ThoPhi/DongHoChu_TiengAnh/CircuitBuffer/eagleUp/eagleUp_ShiftCircuit_board_bottom.png

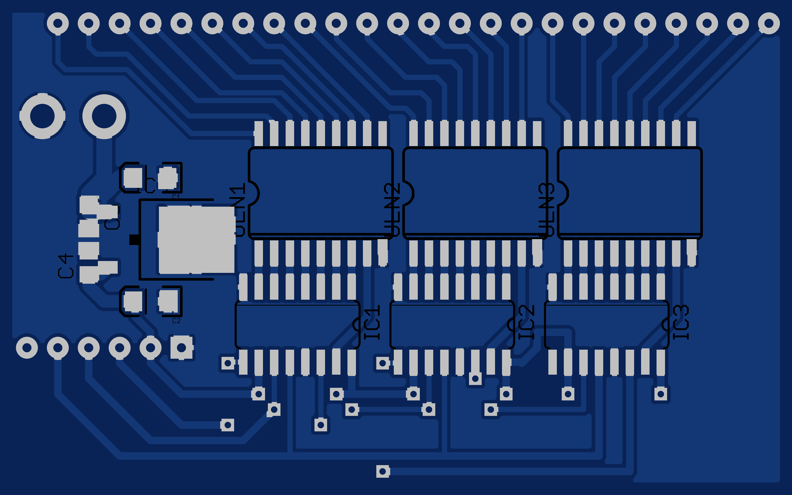
CircuitBuffer/eagleUp/eagleUp_ShiftCircuit_board_bottom.png
