ThoPhi/DongHoChu_TiengAnh/CircuitBuffer/eagleUp/eagleUp_ShiftCircuit_board_top.png

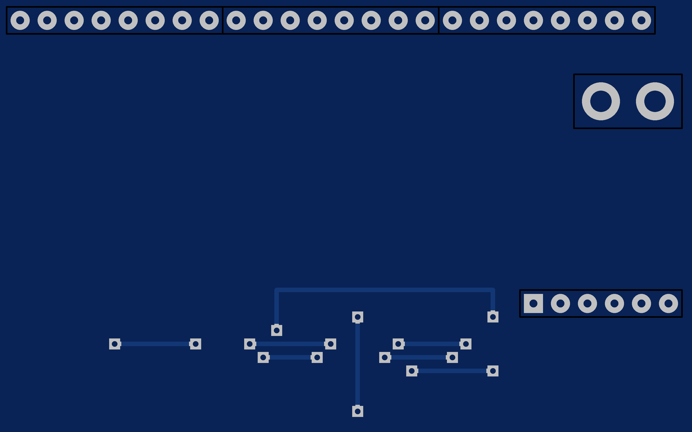
CircuitBuffer/eagleUp/eagleUp_ShiftCircuit_board_top.png
