ThoPhi/DongHoChu_TiengAnh/CircuitBuffer/eagleUp/eagleUp_ShiftCircuit_bottom.png

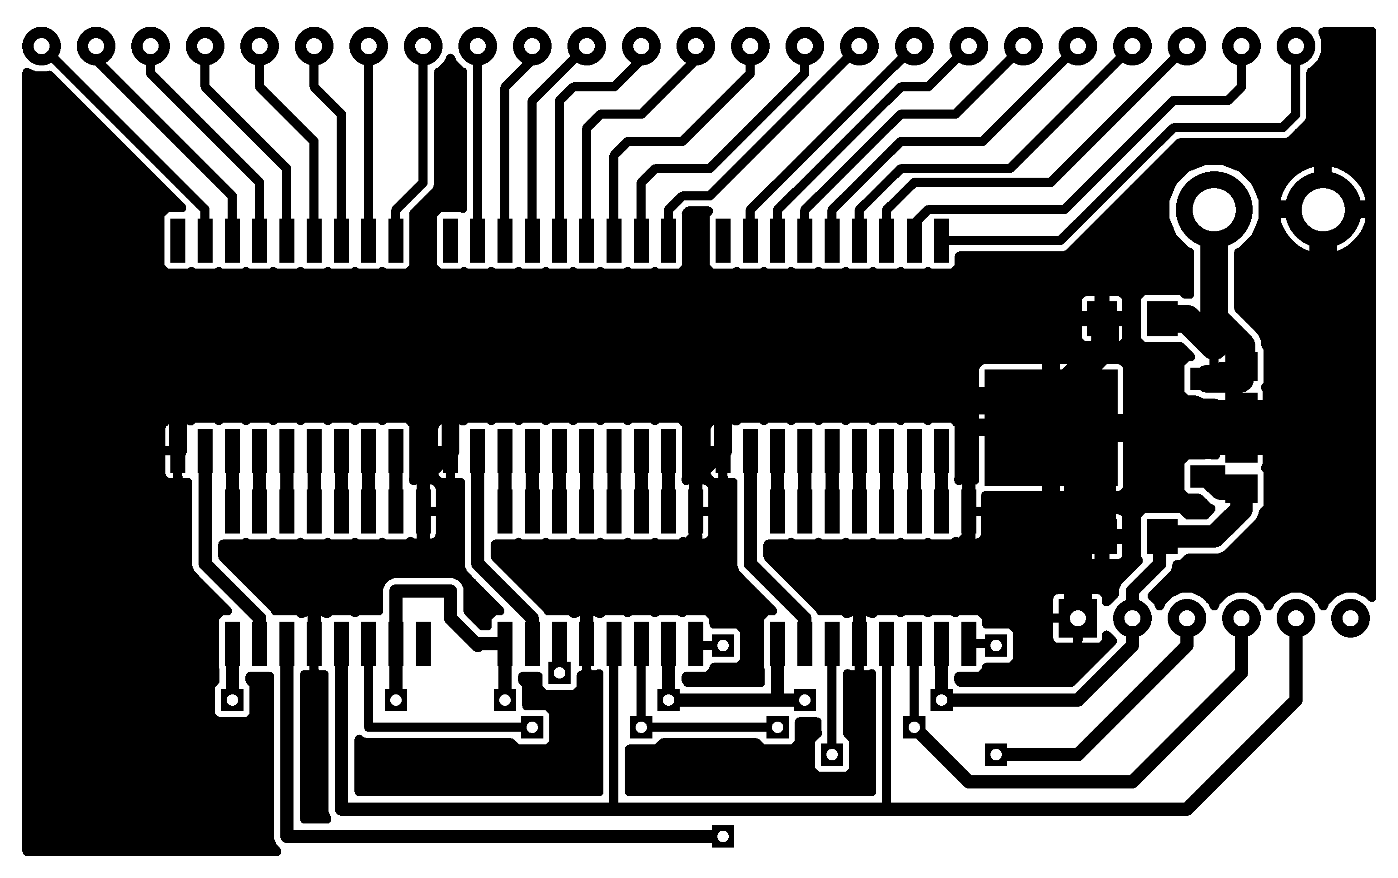
CircuitBuffer/eagleUp/eagleUp_ShiftCircuit_bottom.png
