ThoPhi/DongHoChu_TiengAnh/CircuitBuffer/eagleUp/eagleUp_ShiftCircuit_bottom_mask.png

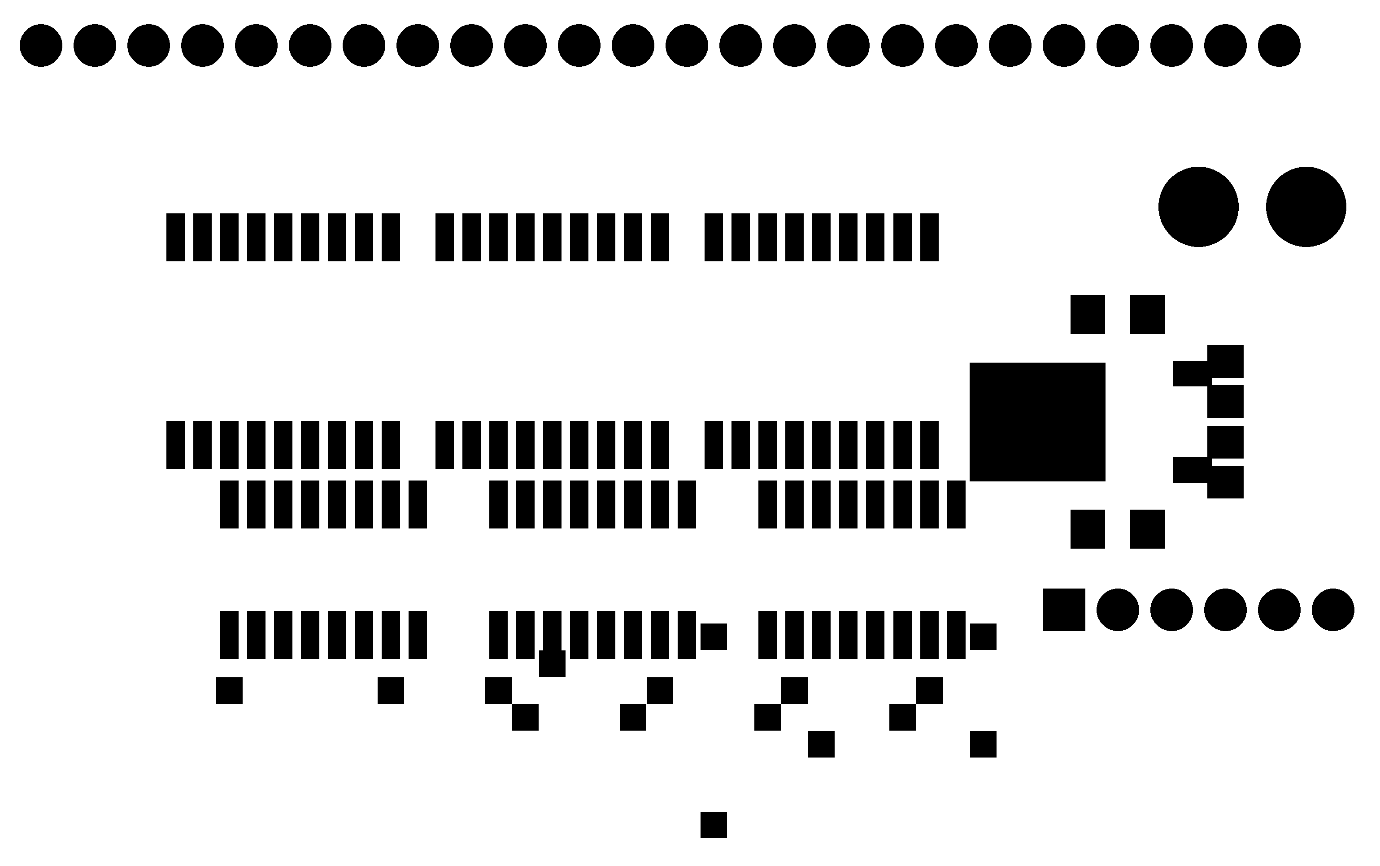
CircuitBuffer/eagleUp/eagleUp_ShiftCircuit_bottom_mask.png
