ThoPhi/DongHoChu_TiengAnh/CircuitBuffer/eagleUp/eagleUp_ShiftCircuit_bottom_silk.png

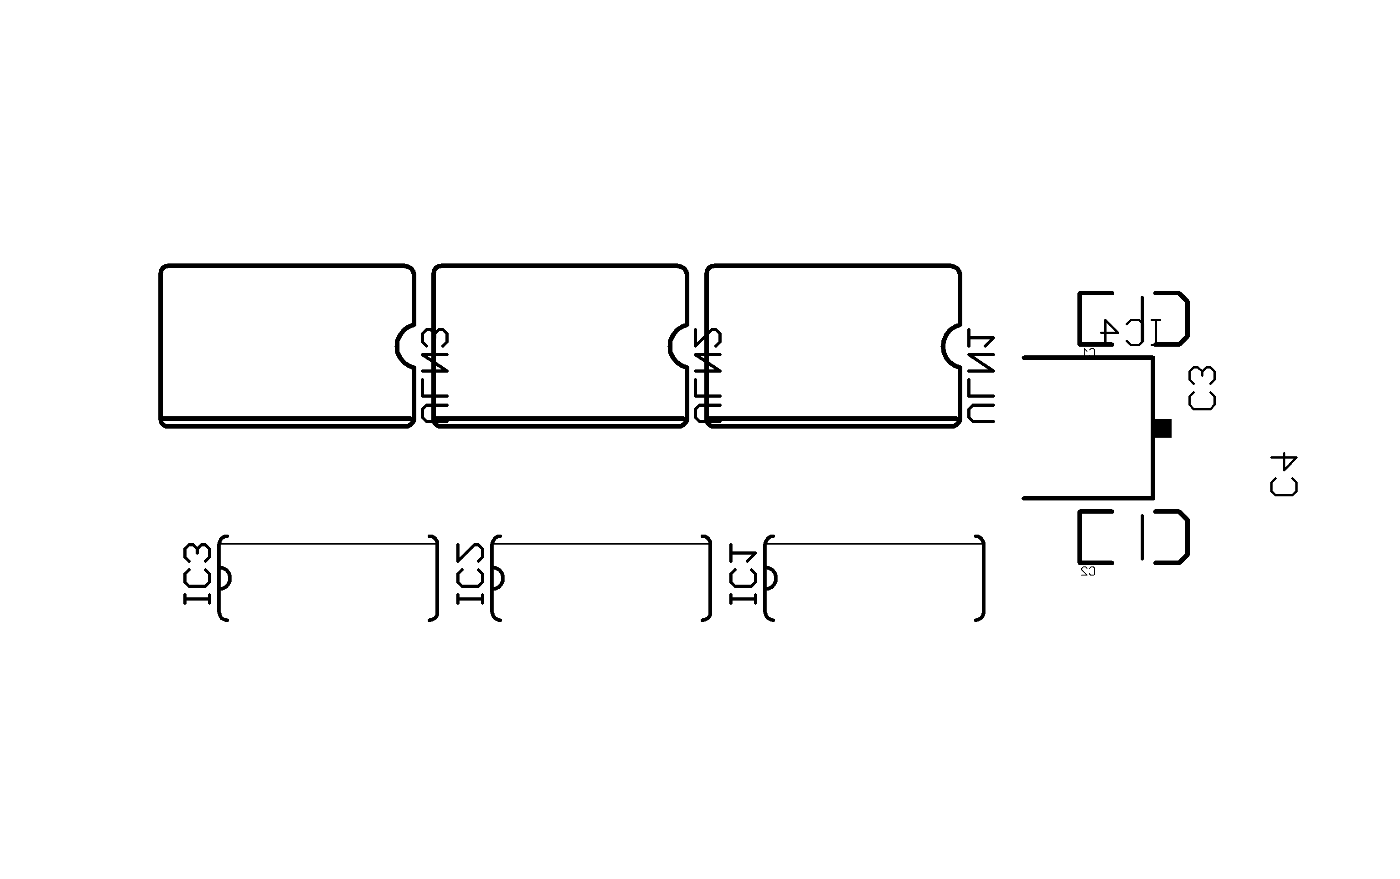
CircuitBuffer/eagleUp/eagleUp_ShiftCircuit_bottom_silk.png
