ThoPhi/DongHoChu_TiengAnh/CircuitBuffer/eagleUp/eagleUp_ShiftCircuit_imagesize.png

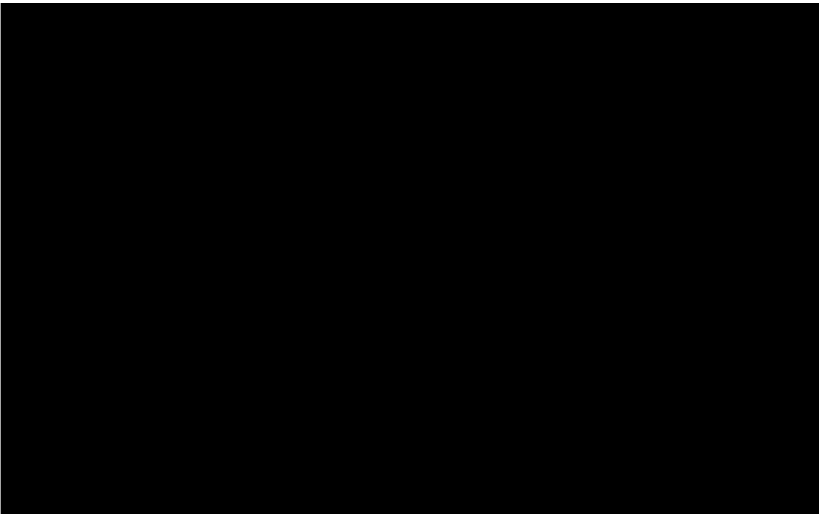
CircuitBuffer/eagleUp/eagleUp_ShiftCircuit_imagesize.png
