ThoPhi/DongHoChu_TiengAnh/CircuitBuffer/eagleUp/eagleUp_ShiftCircuit_outline.png

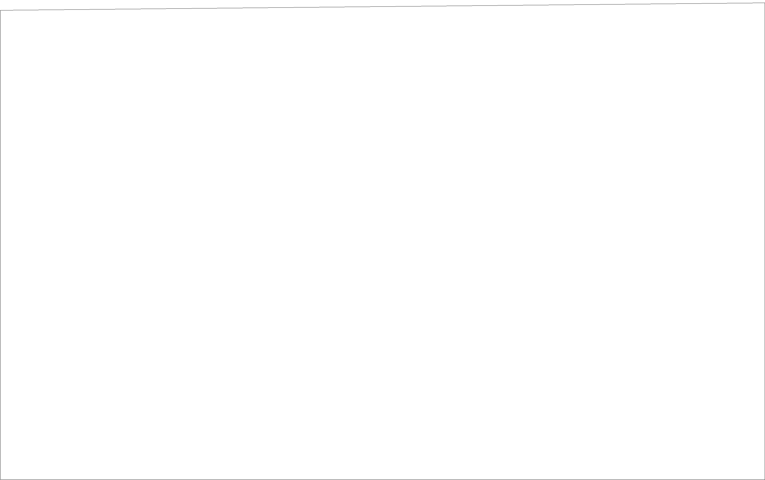
CircuitBuffer/eagleUp/eagleUp_ShiftCircuit_outline.png
