ThoPhi/DongHoChu_TiengAnh/CircuitBuffer/eagleUp/eagleUp_ShiftCircuit_top.png

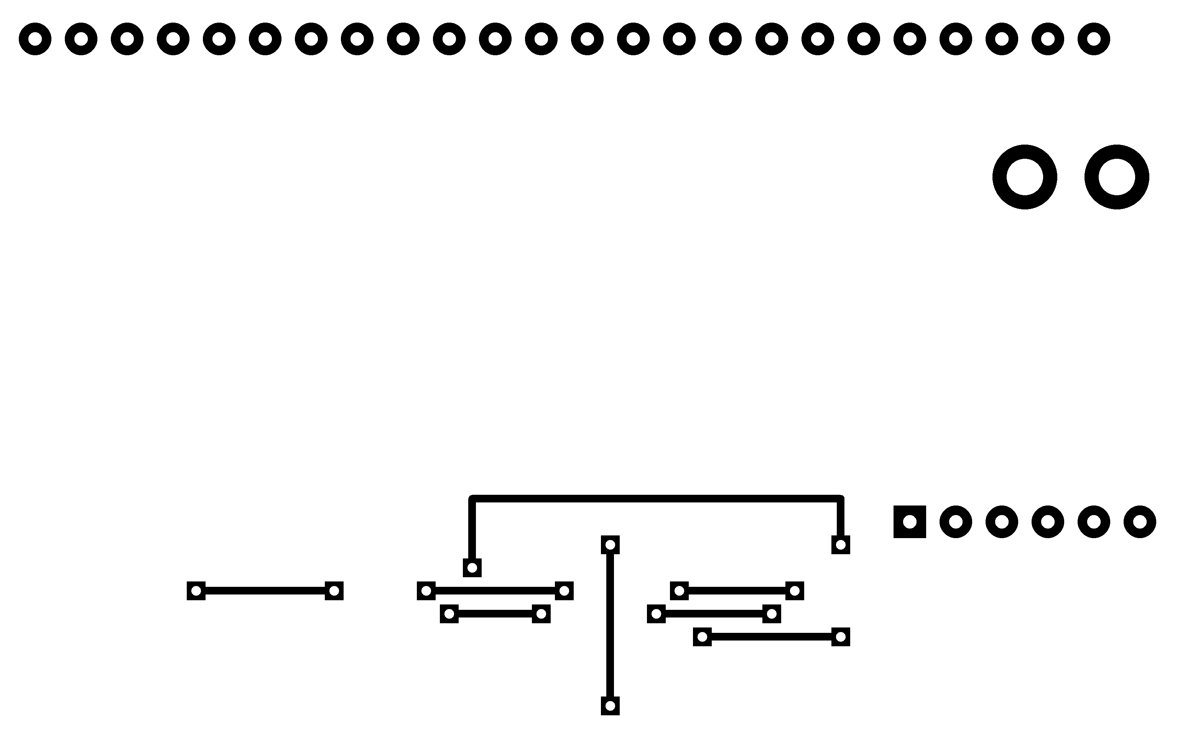
CircuitBuffer/eagleUp/eagleUp_ShiftCircuit_top.png
