ThoPhi/DongHoChu_TiengAnh/CircuitBuffer/eagleUp/eagleUp_ShiftCircuit_top_silk.png

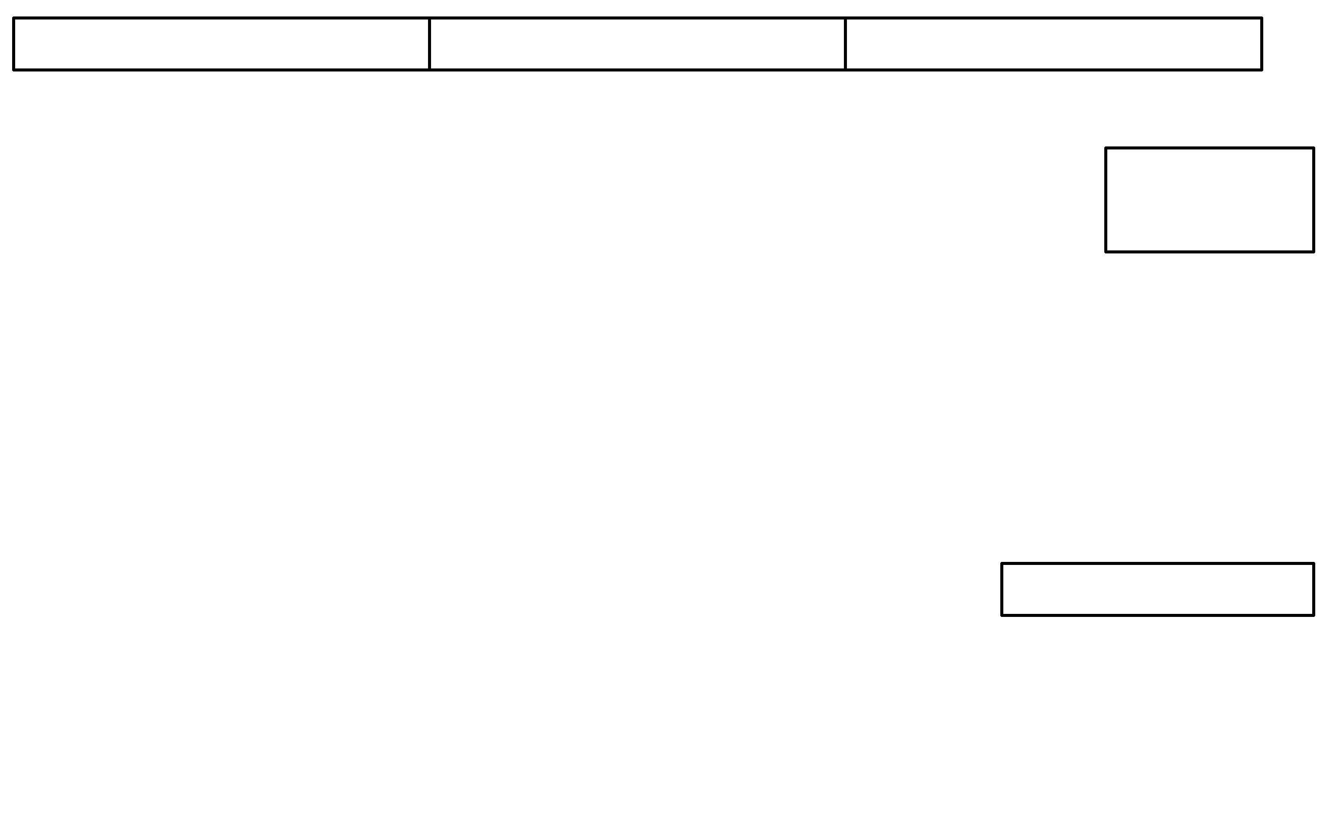
CircuitBuffer/eagleUp/eagleUp_ShiftCircuit_top_silk.png
