ThoPhi/DongHoChu_TiengAnh/Images/2014-12-19 15.57.03.jpg

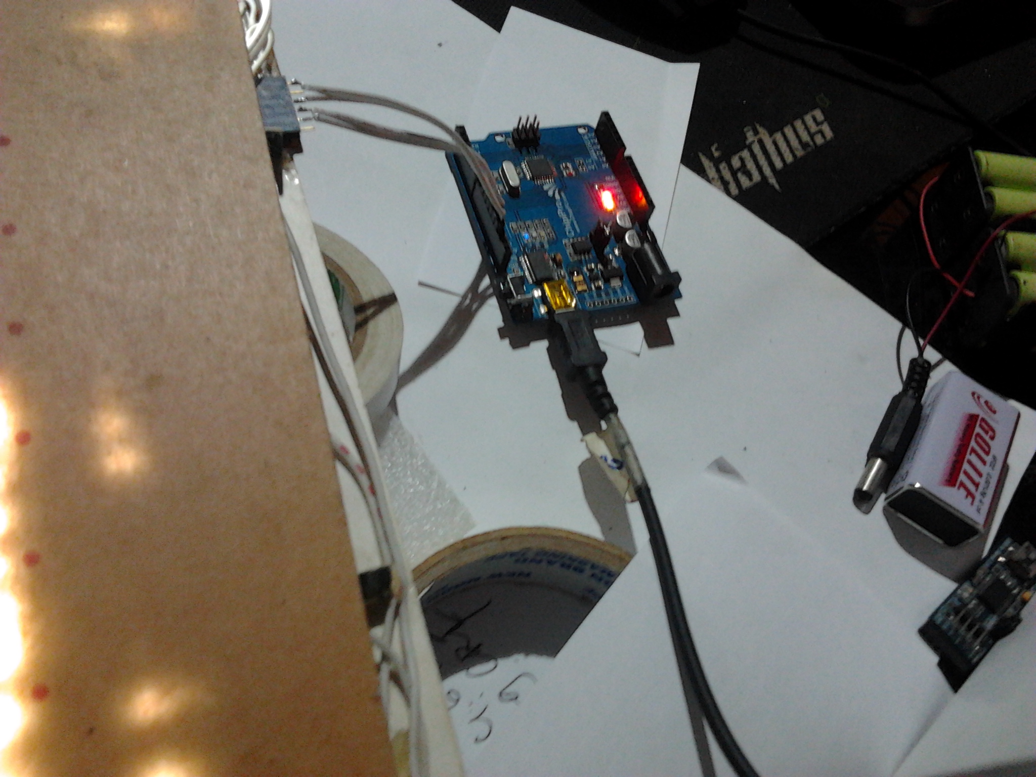
Images/2014-12-19 15.57.03.jpg
