ThoPhi/DongHoChu_TiengAnh/Images/2014-12-19 17.26.58.jpg

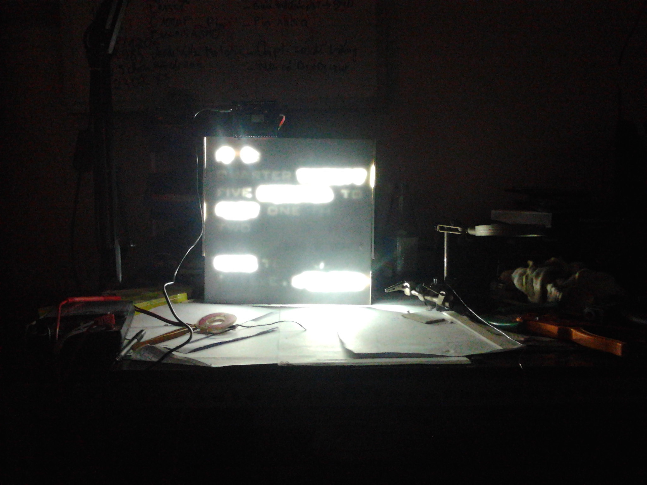
Images/2014-12-19 17.26.58.jpg
